Meyer2211/SACFC/SWIR/Analisis_Bandas_de_soporte/analisis_bandas/analisis_separabilidad.png

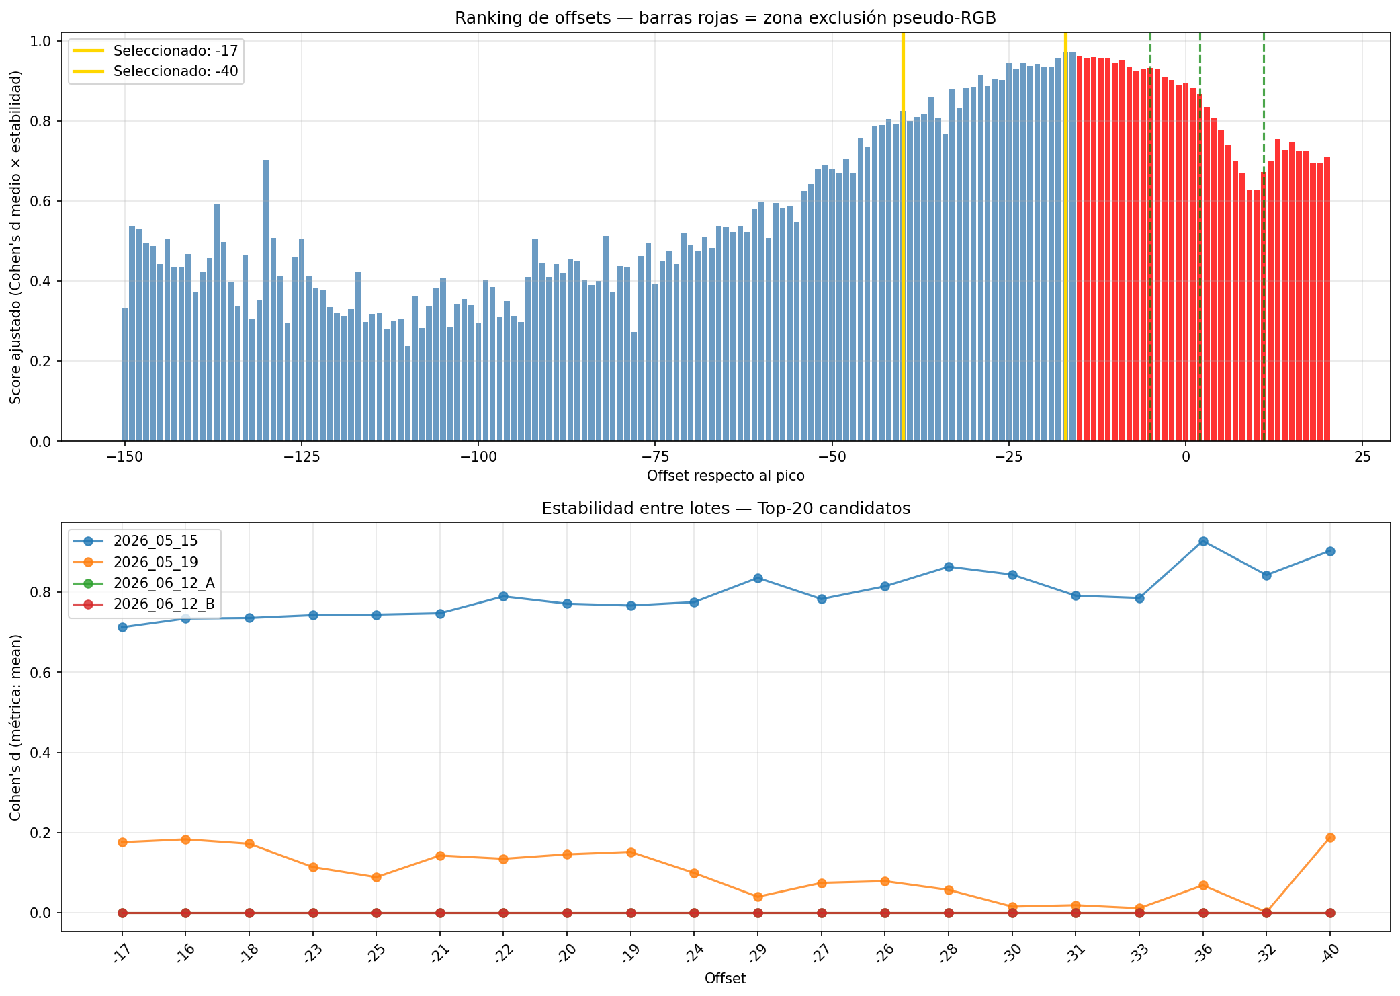
SWIR/Analisis_Bandas_de_soporte/analisis_bandas/analisis_separabilidad.png
