Meyer2211/SACFC/RGB/Pruebas_Obtenidas/Image_processing/PAD_Dinamico/mandarina_4_MALA.jpg

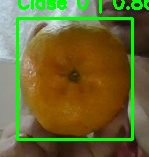
RGB/Pruebas_Obtenidas/Image_processing/PAD_Dinamico/mandarina_4_MALA.jpg
