Meyer2211/SACFC/RGB/Pruebas_Obtenidas/Image_processing/PAD_Dinamico/mandarina_6_MALA.jpg

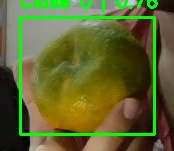
RGB/Pruebas_Obtenidas/Image_processing/PAD_Dinamico/mandarina_6_MALA.jpg
