Meyer2211/SACFC/RGB/Pruebas_Obtenidas/Image_processing/PAD_Dinamico/mandarina_8_MALA.jpg

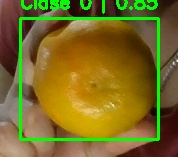
RGB/Pruebas_Obtenidas/Image_processing/PAD_Dinamico/mandarina_8_MALA.jpg
