Meyer2211/SACFC/RGB/Pruebas_Obtenidas/Image_processing/PAD_Normal/mandarina_2_BUENA.jpg

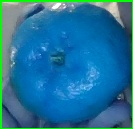
RGB/Pruebas_Obtenidas/Image_processing/PAD_Normal/mandarina_2_BUENA.jpg
