Meyer2211/SACFC/SWIR/Pruebas_del_sistema_02_06_26/4_02_06_26.jpeg

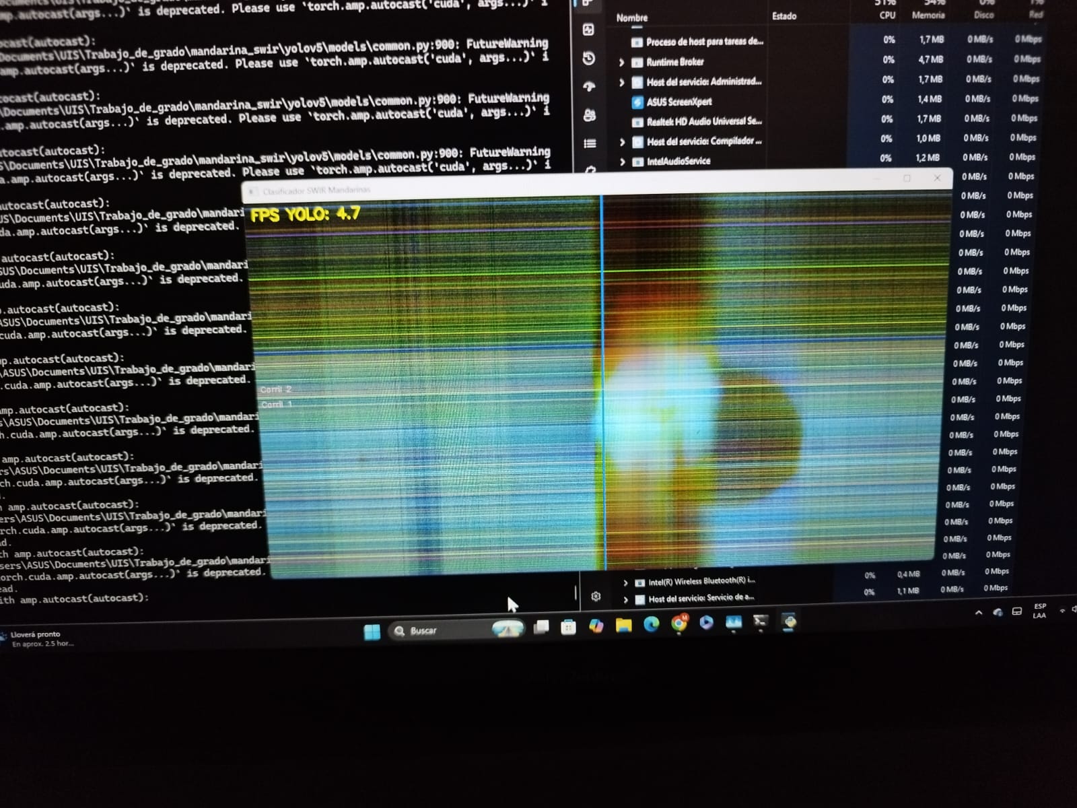
SWIR/Pruebas_del_sistema_02_06_26/4_02_06_26.jpeg
